avadsariya0-coder/DROPDECK/GALLERY/BACK RENDER.png

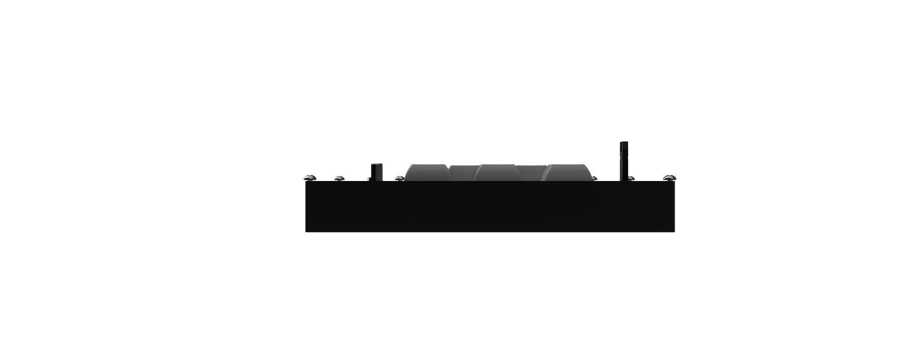
GALLERY/BACK RENDER.png
