avadsariya0-coder/DROPDECK/GALLERY/BOTTOM RENDER.png

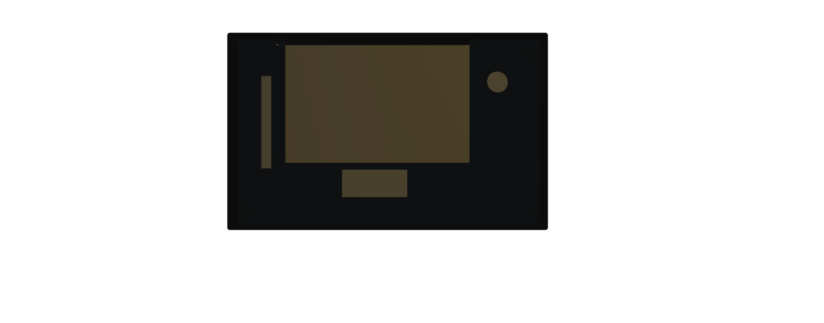
GALLERY/BOTTOM RENDER.png
